alarisnu/7dof_arm_tracker/CAD models/Part2.SLDPRT

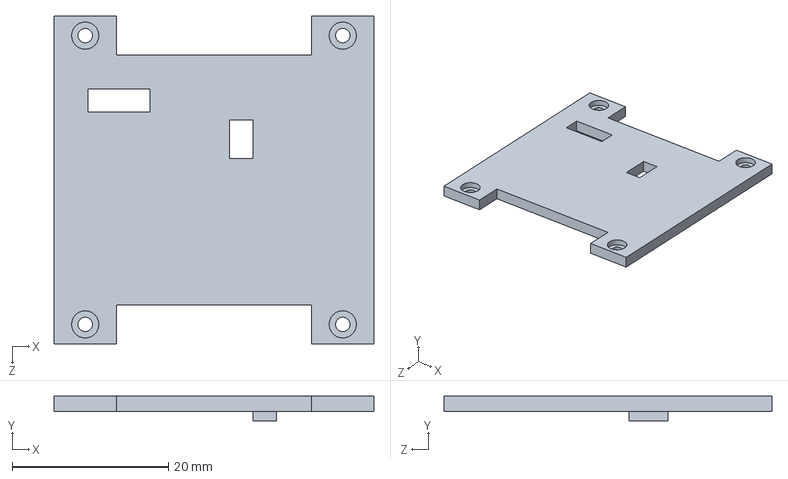
[picture p15: CAD file, 2020-05-13]
CAD models/Part2.SLDPRT
41.0 x 3.20 x 42.0 mm
